reseauducommun/cociclo/cociclo_Mexico/hardware/circuit/cociclo_circuit imprimé.jpg

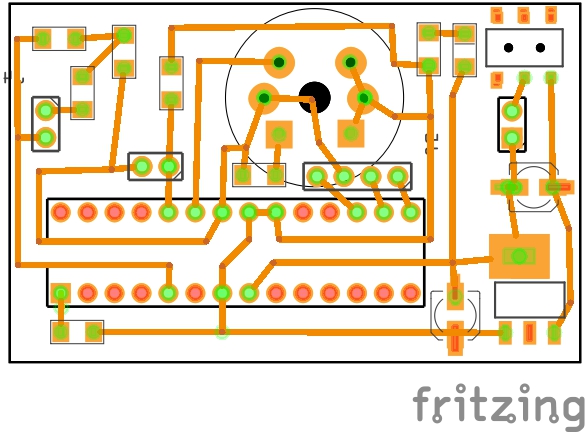
cociclo_Mexico/hardware/circuit/cociclo_circuit imprimé.jpg
