reseauducommun/cociclo/cociclo_transpiksel_eastern_bloc/cociclo_point_acces_EN.pdf

1. Go to:

http://fr.mygeoposition.com/

and note your position (latitude + longitude)

2. Power your cociclo
3. Log in to the 'cociclo' access point, the password is 'placecommune'

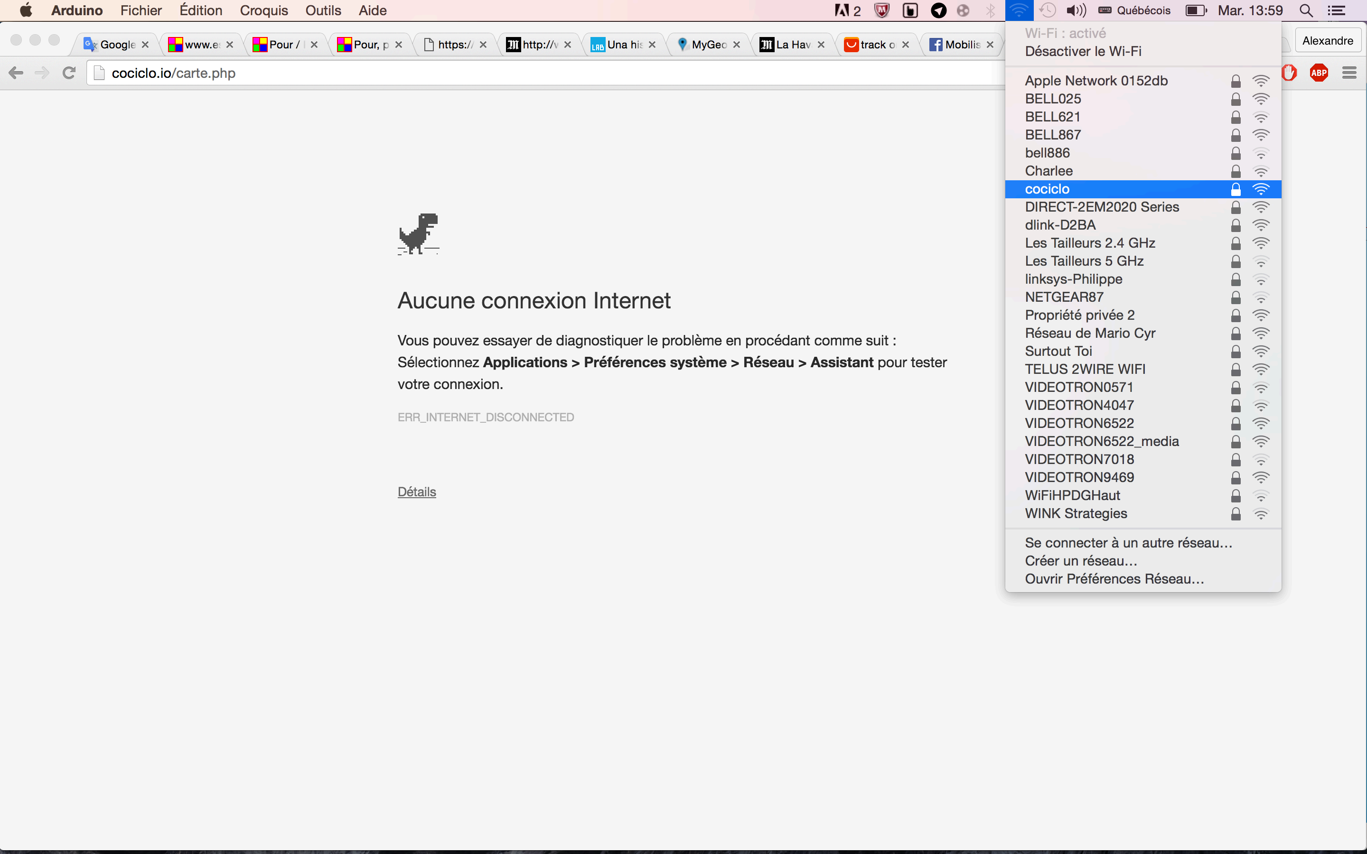
[picture p3: figure]

4. Open a new web page or enter this address : 192.168.4.1. Choose ‘Configure WIFI’ :

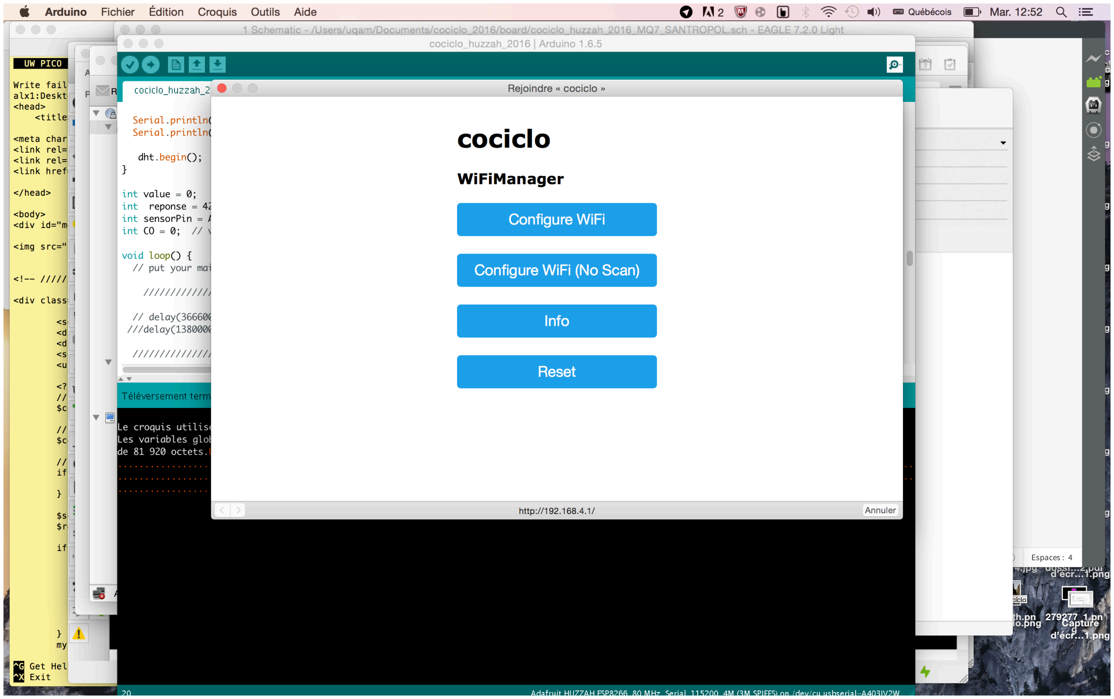
[picture p4: figure]

5. Select your home access point and enter your password, choose a name for your cociclo (no special characters or spaces) the latitude and longitude of your cociclo.

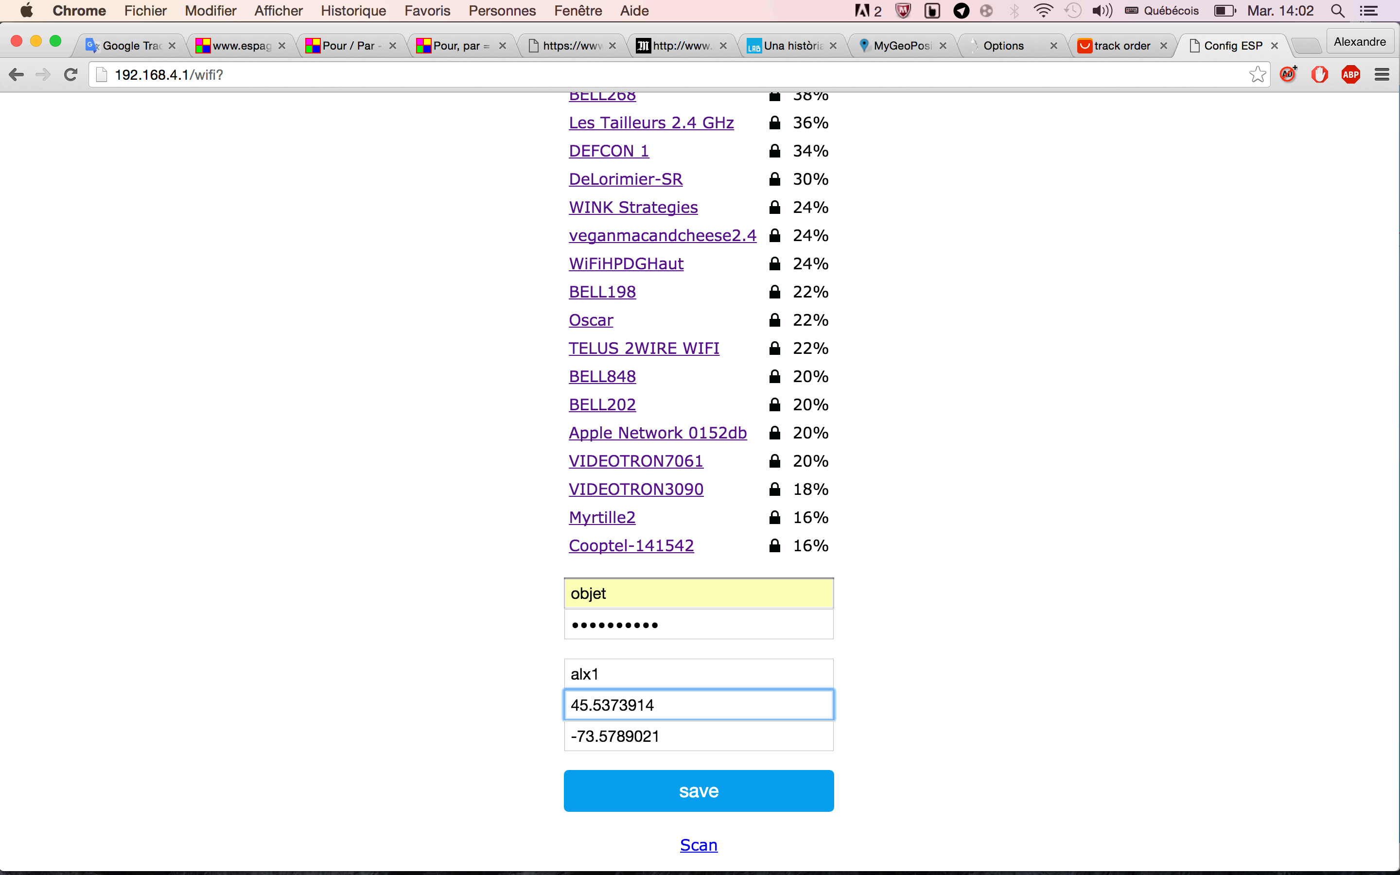
[picture p5: figure]

6. Restart your cociclo
7. Wait for 25 minutes (to heat the CO sensor and avoid false readings) skip this point if the cociclo is not configured with this long pause.
8. Go to http://cociclo.io/carte.php and see your cocíclo on the map.
9. Send an image of your installation.

If there’s a problem, send a mail to : acastonguay@artengine.ca
