reseauducommun/cociclo/cociclo_Mexico/hardware/mexico/cociclo_mexico_etch_silk_top.pdf

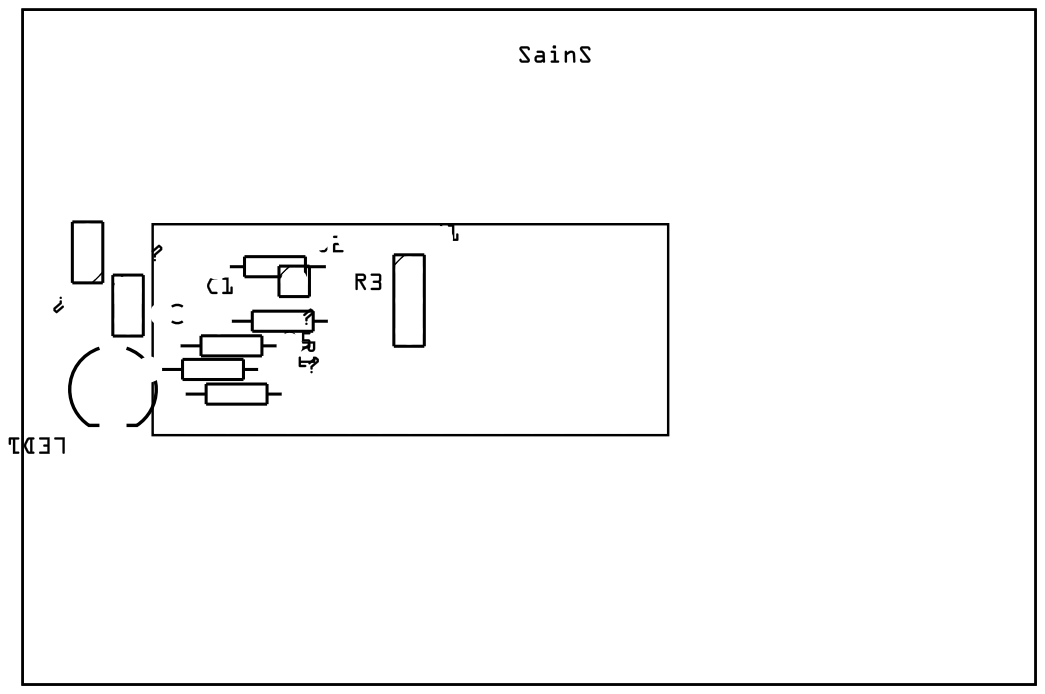
[picture p6: page 1]
