reseauducommun/cociclo/cociclo_Mexico/hardware/mexico/cociclo_mexico_etch_silk_top_mirror.pdf

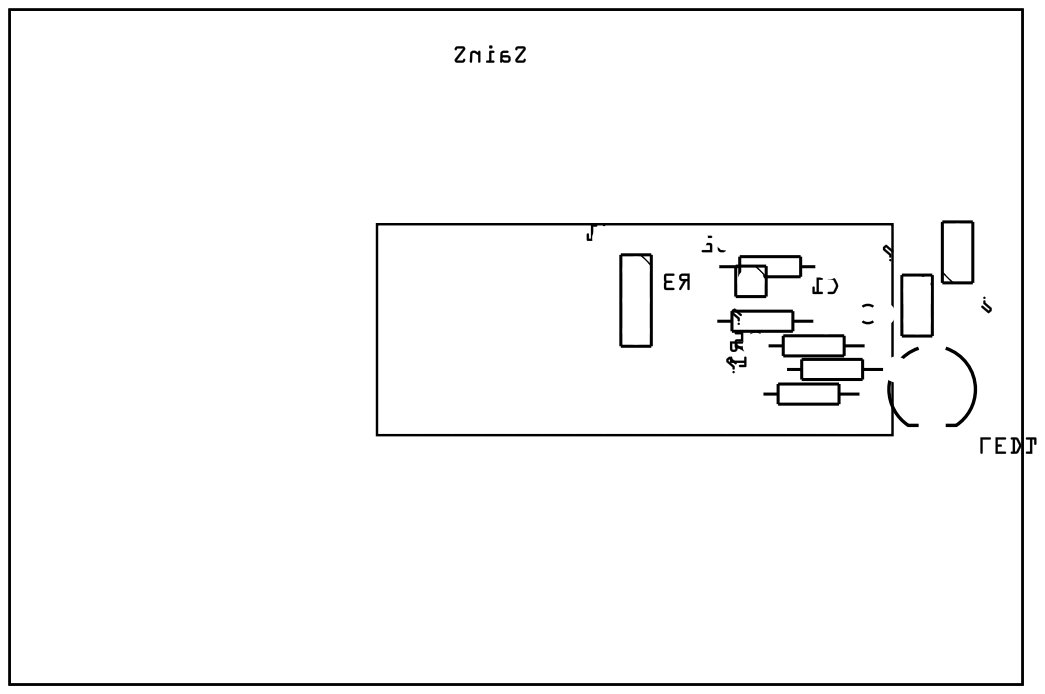
[picture p7: page 1]
