reseauducommun/cociclo/cociclo_Mexico/hardware/circuit/hey/cociclo_etch_paste_mask_bottom.pdf

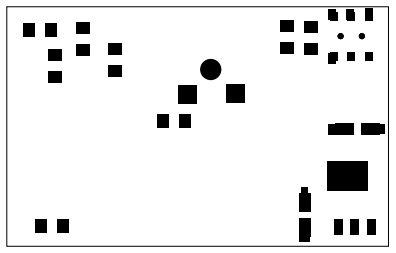
[picture p8: figure]
