reseauducommun/cociclo/cociclo_Mexico/hardware/circuit/hey/cociclo_etch_paste_mask_bottom_mirror.pdf

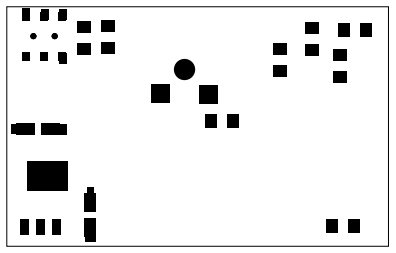
[picture p9: figure]
