reseauducommun/cociclo/cociclo_Mexico/hardware/mexico/mexicoDF/cociclo_mexico_etch_silk_top.pdf

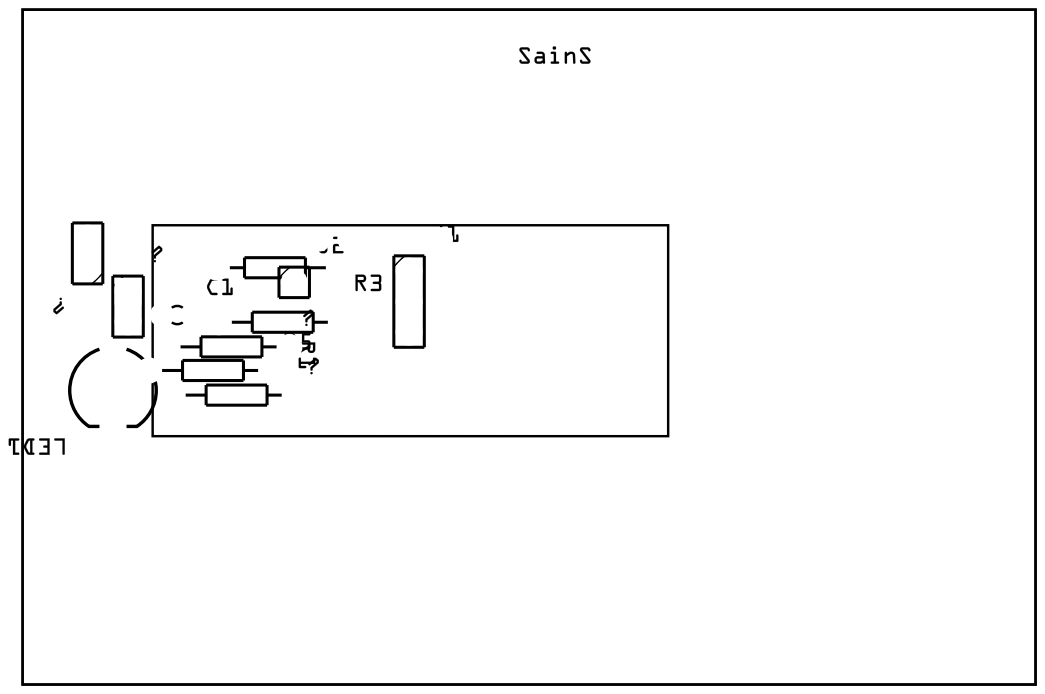
[picture p10: page 1]
