reseauducommun/cociclo/cociclo_Mexico/hardware/mexico/mexicoDF/cociclo_mexico_etch_silk_top_mirror.pdf

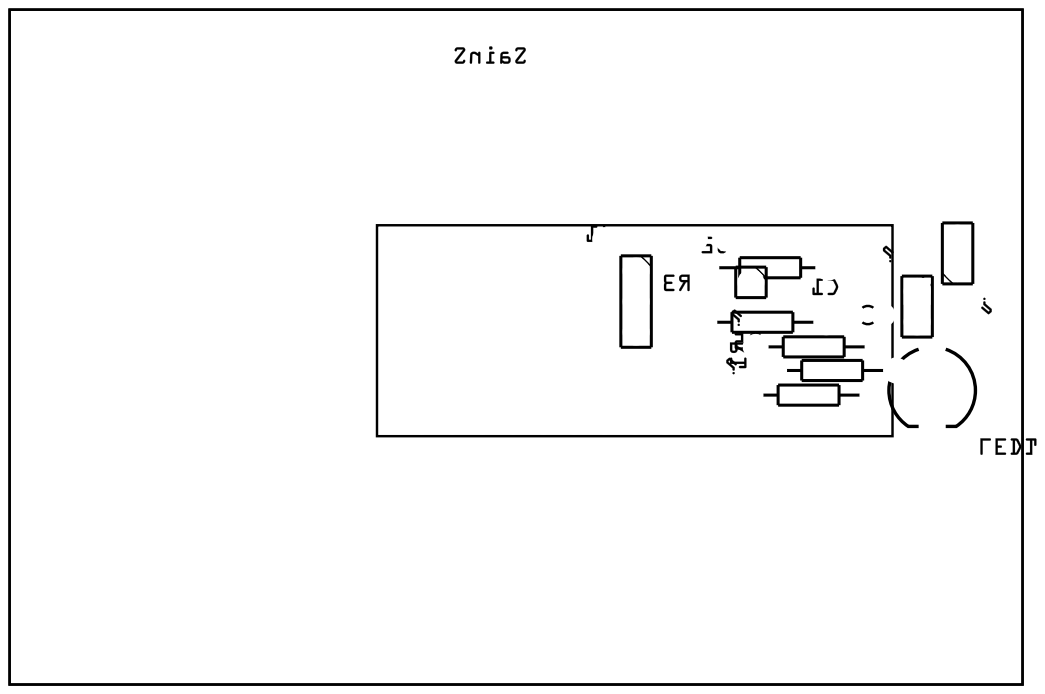
[picture p11: page 1]
