reseauducommun/cociclo/cociclo_placeCommune/software/cociclo_point_acces_p.pdf

1. Allez à':'

http://fr.mygeoposition.com/

et'notez'votre'position'

2. Branchez'votre'cocíclo'
3. Branchez votre'ordinateur'sur'le'point'd'accès''cociclo','le'mot'de passe'est''placecommune''

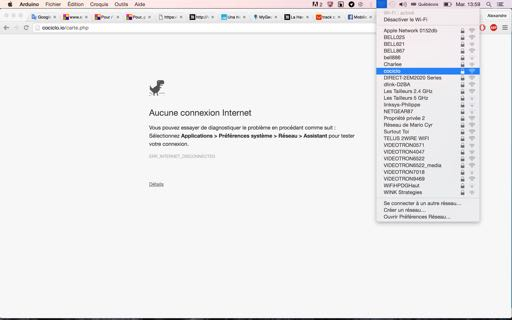
[picture p12: figure]

4.'Ouvrez'une'page'de'navigateur'et'allez'à'192.168.4.1'(ou tentez'd'accéder'à'n'importe'qu'elle'page).'Choisir' ‘Configure'WIFI’ :

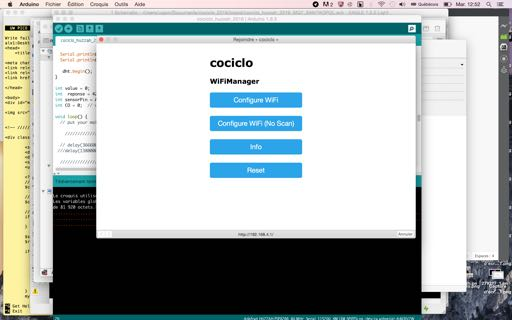
[picture p13: figure]

5.'Choisissez'un'nom'd'utilisateur,'entrez'votre'nom'de'point'd'accès'au'réseau'et'son'mot'de'passe'ainsi'que' la'latitude'et'la'longitude'de'la'position'de'votre'cocíclo.

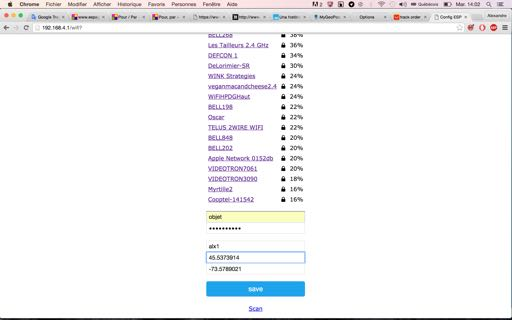
[picture p14: figure]

6.'Redémarrez'votre'cocíclo'

7.'Patientez 25'minutes (le'temps'de'réchauffer'le'capteur'de'CO'afin'd’éviter'les'mauvaises'lectures,'allez'à'la' page'http://cociclo.io/carte.php et'trouvez'les'valeurs'de'votre'cocíclo'

8.'Postez'une'image'de'l'endroit'où'vous'avez'installé'votre'cocíclo.'

En'cas'de'problème,'contactezYmoi'à'acastonguay@artengine.ca
