reseauducommun/cociclo/cociclo_03/hardware/eagleUp/01/eagleUp_cociclo_03_top_silk.png

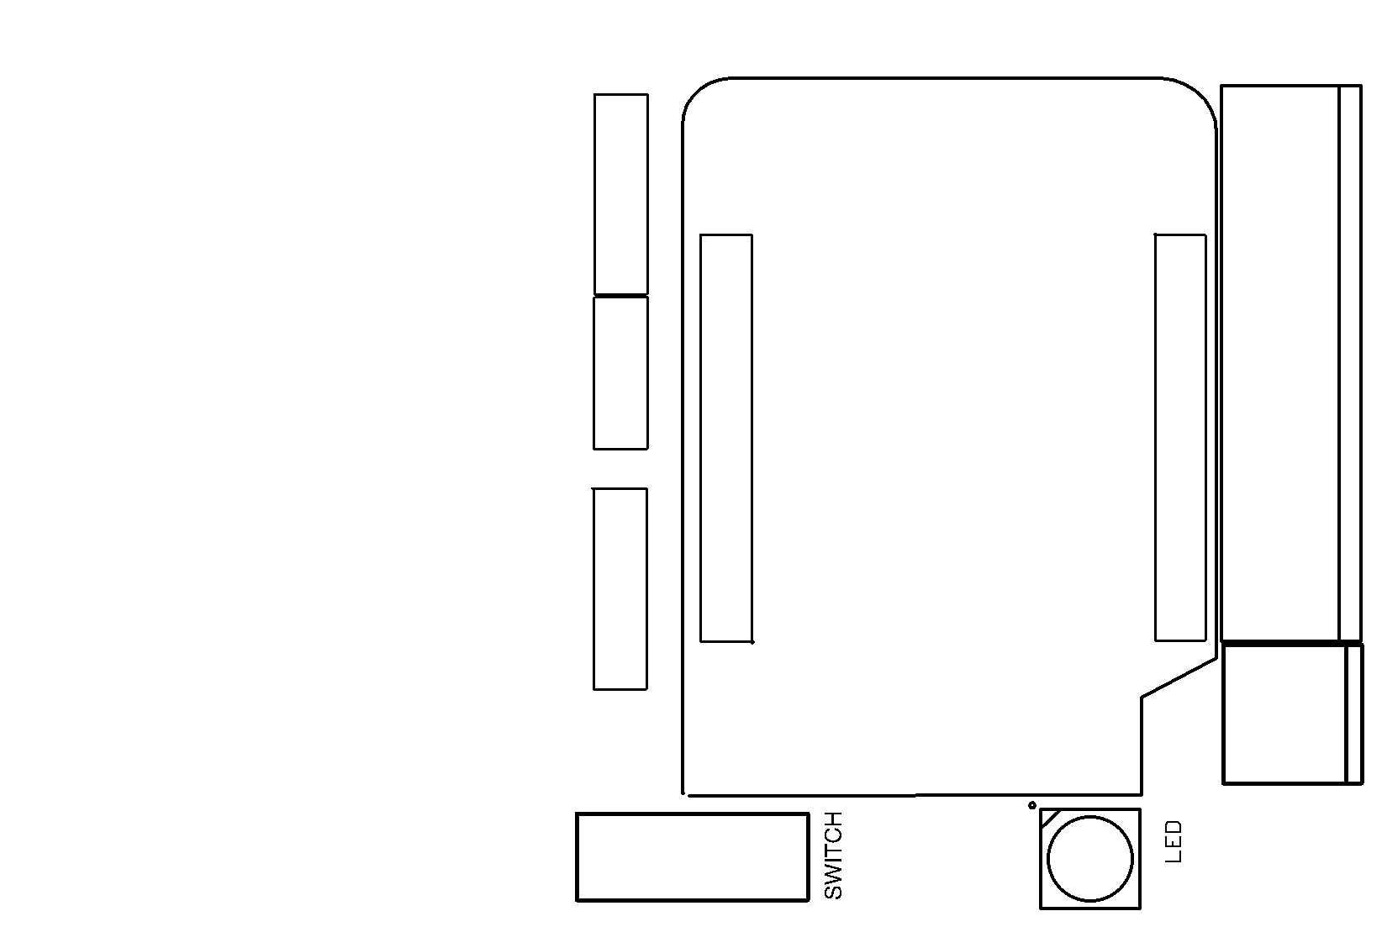
cociclo_03/hardware/eagleUp/01/eagleUp_cociclo_03_top_silk.png
