reseauducommun/cociclo/cociclo_03/hardware/PMS3003_connections.png

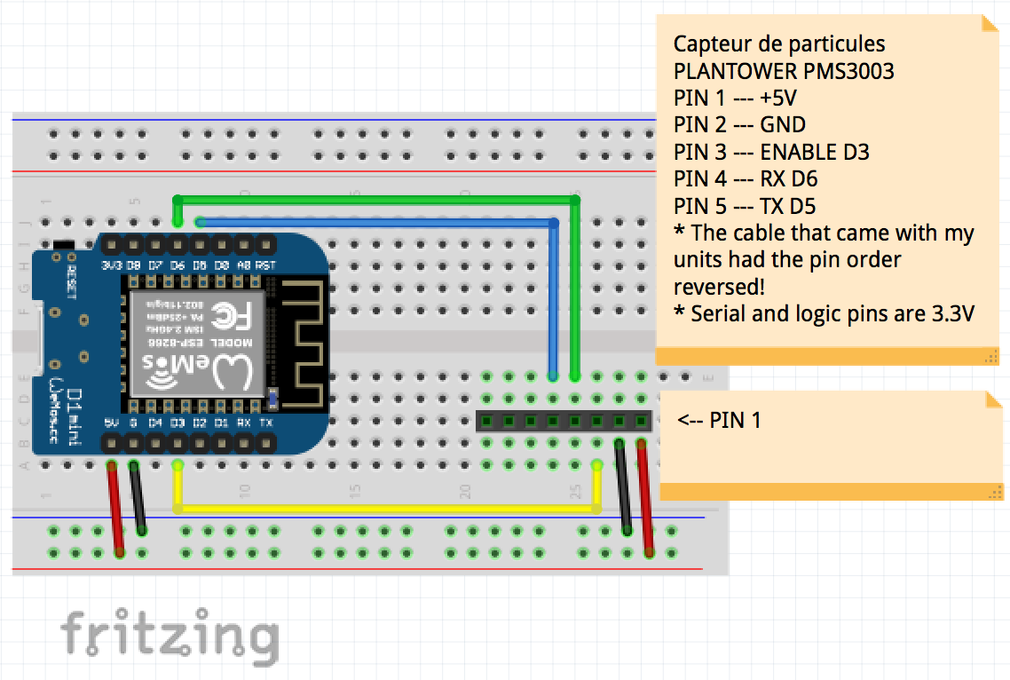
cociclo_03/hardware/PMS3003_connections.png
