reseauducommun/cociclo/cociclo_03/images/cociclo_0_3.jpg

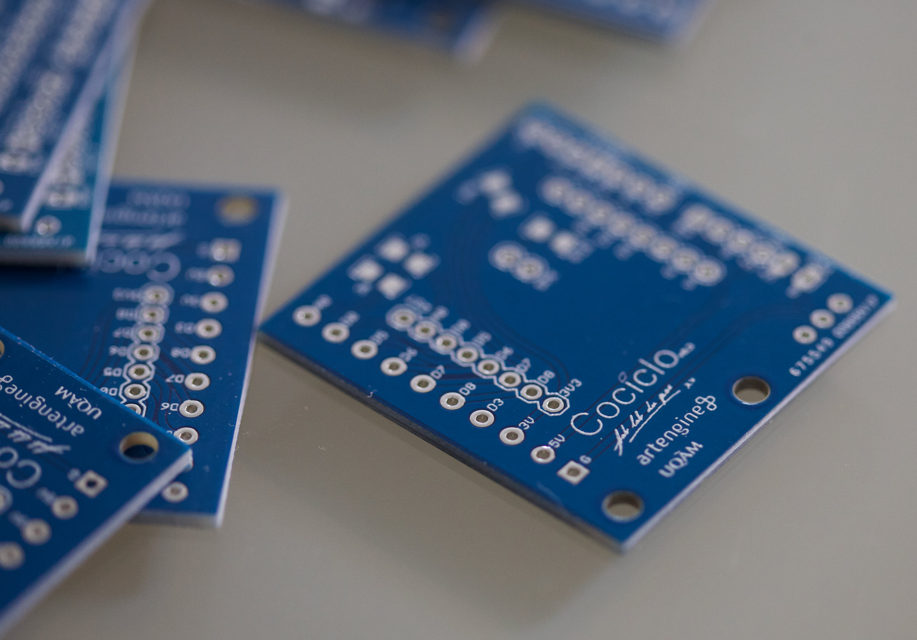
cociclo_03/images/cociclo_0_3.jpg
