reseauducommun/cociclo/cociclo_03/images/eagle_board_capture.png

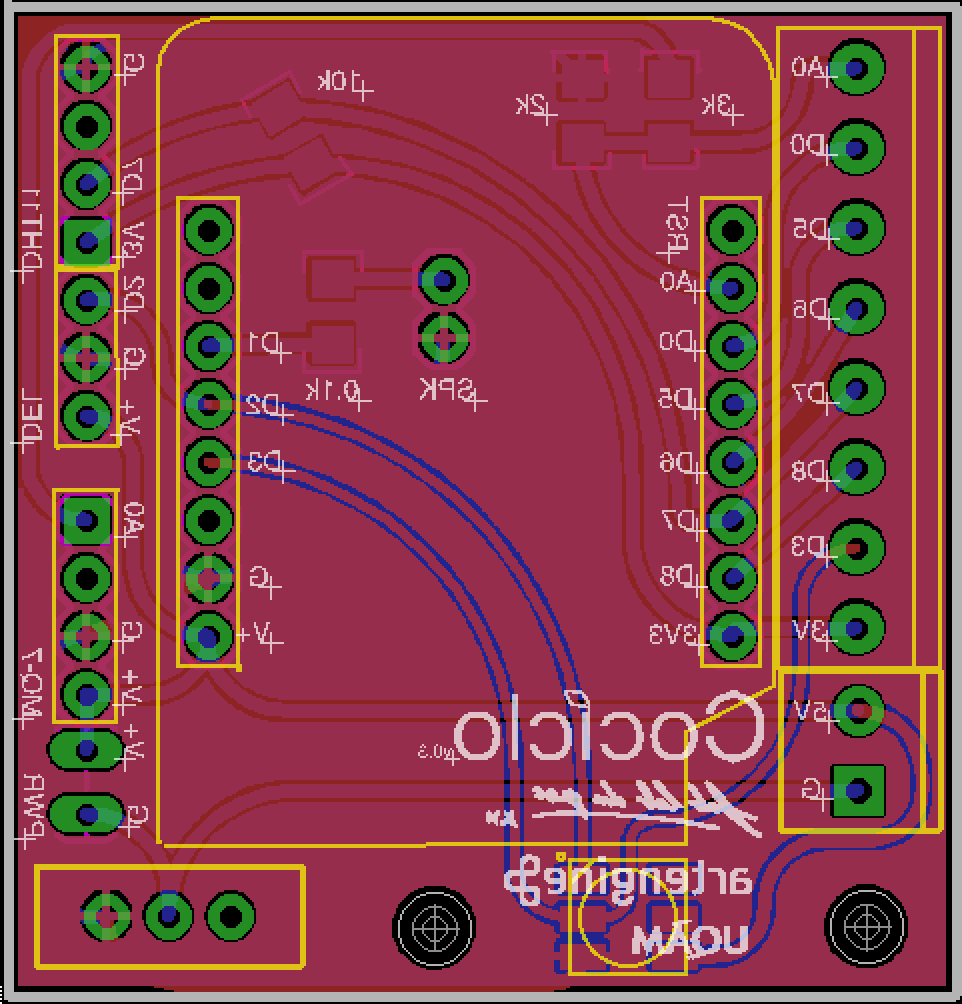
cociclo_03/images/eagle_board_capture.png
