reseauducommun/cociclo/cociclo_cordova/platforms/android/assets/www/img/submerge.png

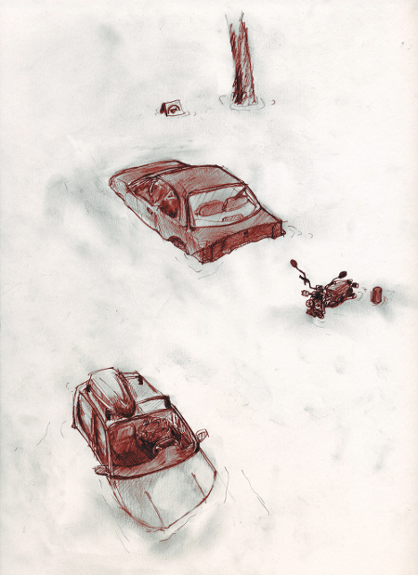
cociclo_cordova/platforms/android/assets/www/img/submerge.png
