reseauducommun/cociclo/cociclo_flowchart.png

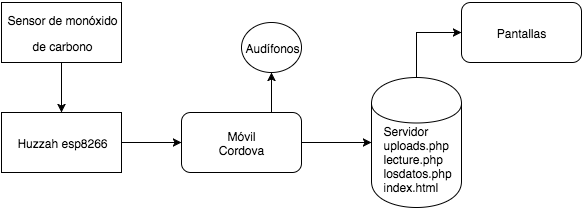
cociclo_flowchart.png
