reseauducommun/cociclo/cociclo_hardware/cociclo_bergen_stencil.png

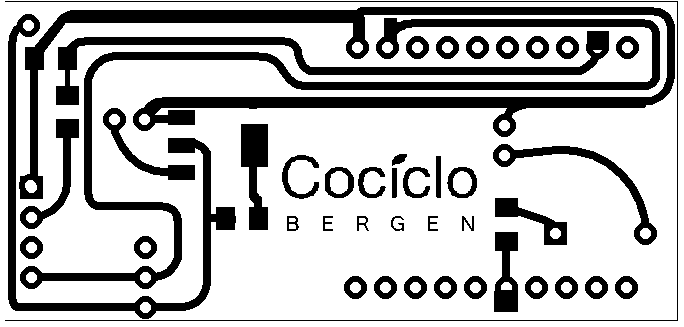
cociclo_hardware/cociclo_bergen_stencil.png
