reseauducommun/cociclo/cociclo_Mexico/hardware/instructions/CTIA_OMTP_Pinout_thumb.png

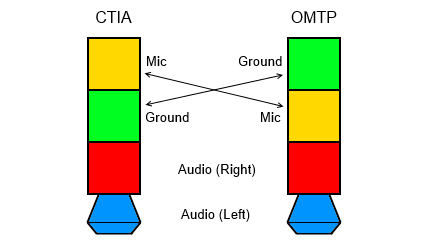
cociclo_Mexico/hardware/instructions/CTIA_OMTP_Pinout_thumb.png
