reseauducommun/cociclo/cociclo_placeCommune/boitier/fond_cociclo_wemos.jpg

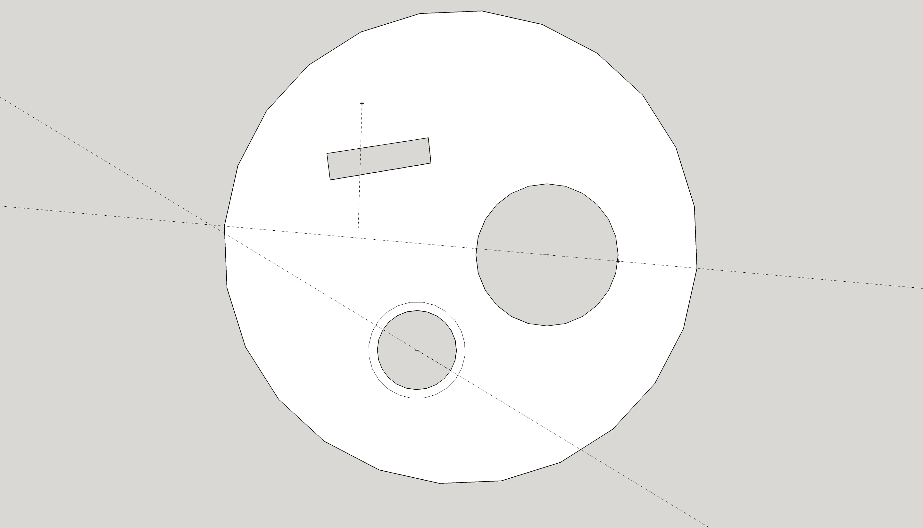
cociclo_placeCommune/boitier/fond_cociclo_wemos.jpg
