reseauducommun/cociclo/cociclo_placeCommune/hardware/cociclo_2016.png

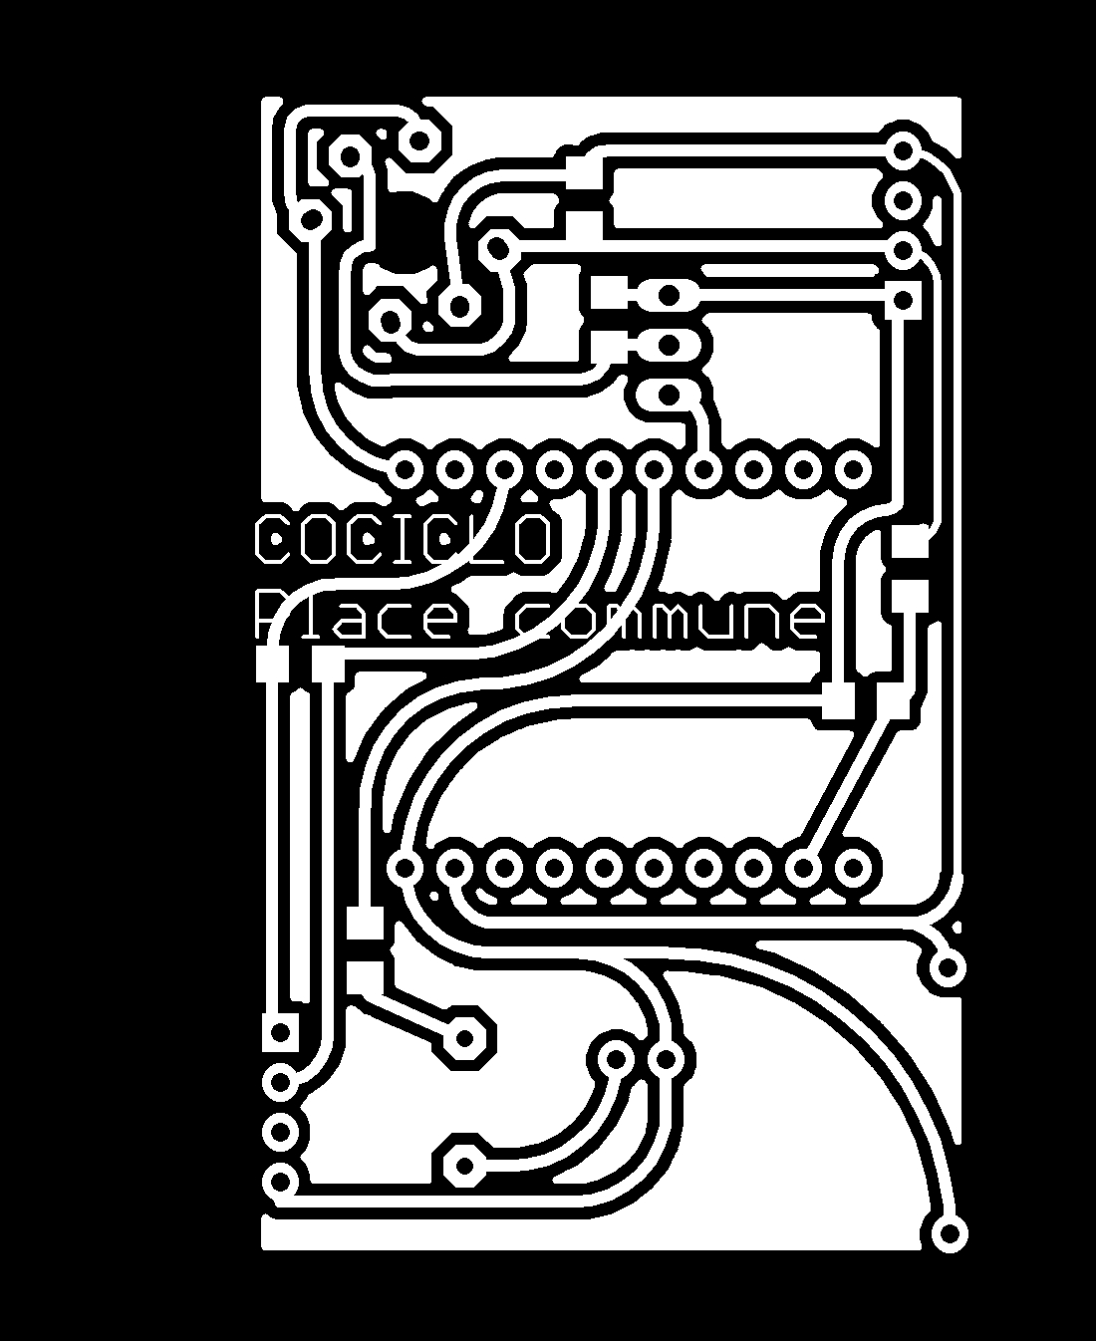
cociclo_placeCommune/hardware/cociclo_2016.png
