reseauducommun/cociclo/cociclo_placeCommune/hardware/cociclo_plaeCommune_composantes.png

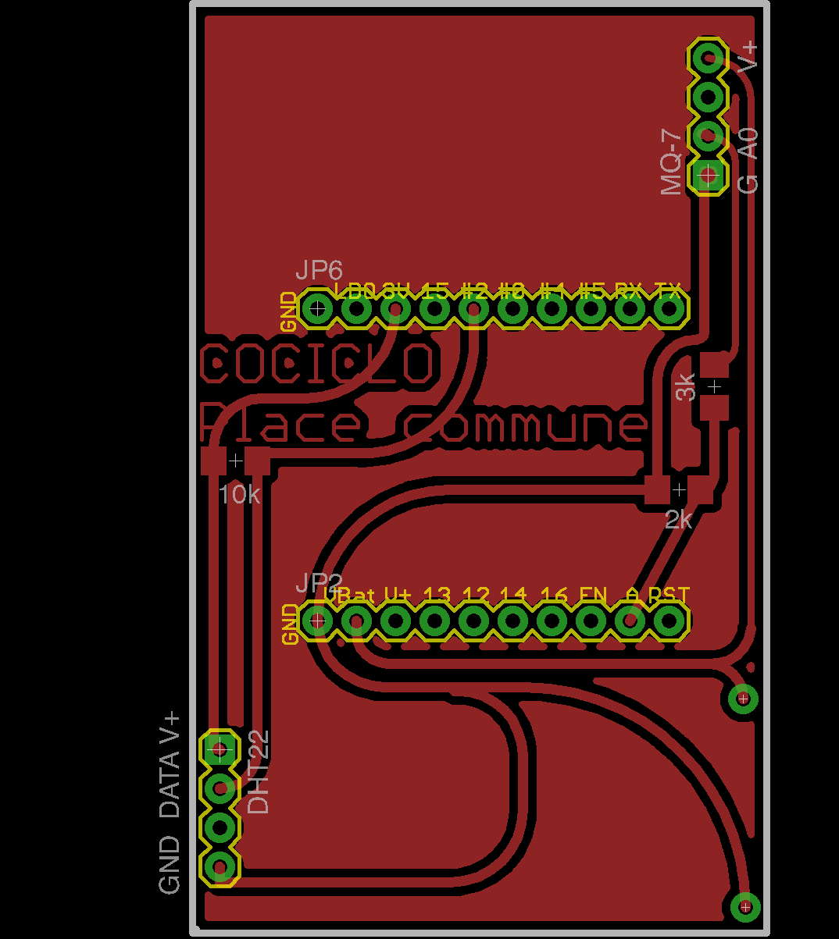
cociclo_placeCommune/hardware/cociclo_plaeCommune_composantes.png
