reseauducommun/cociclo/cociclo_placeCommune/hardware/sainsmart_MQ7.jpg

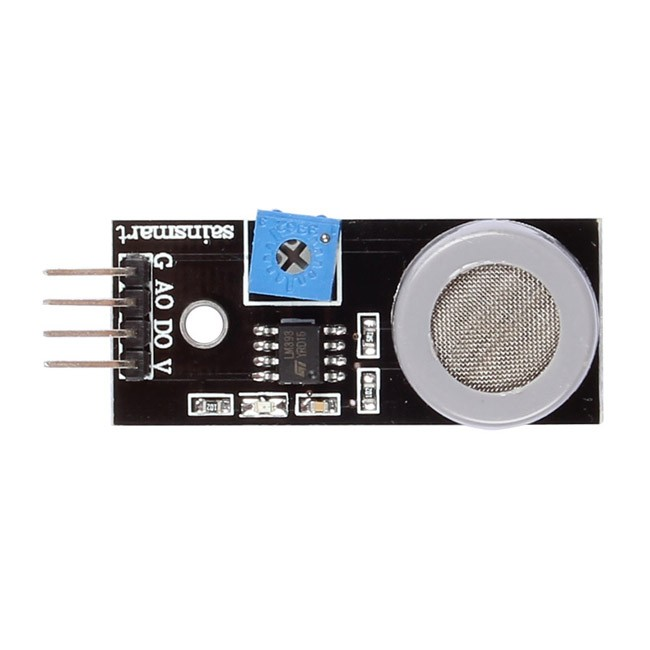
cociclo_placeCommune/hardware/sainsmart_MQ7.jpg
