reseauducommun/cociclo/cociclo_Mexico/hardware/instructions/instructions.pdf

Cocíclo v.

0.42

(Cali

noviembre

2014)

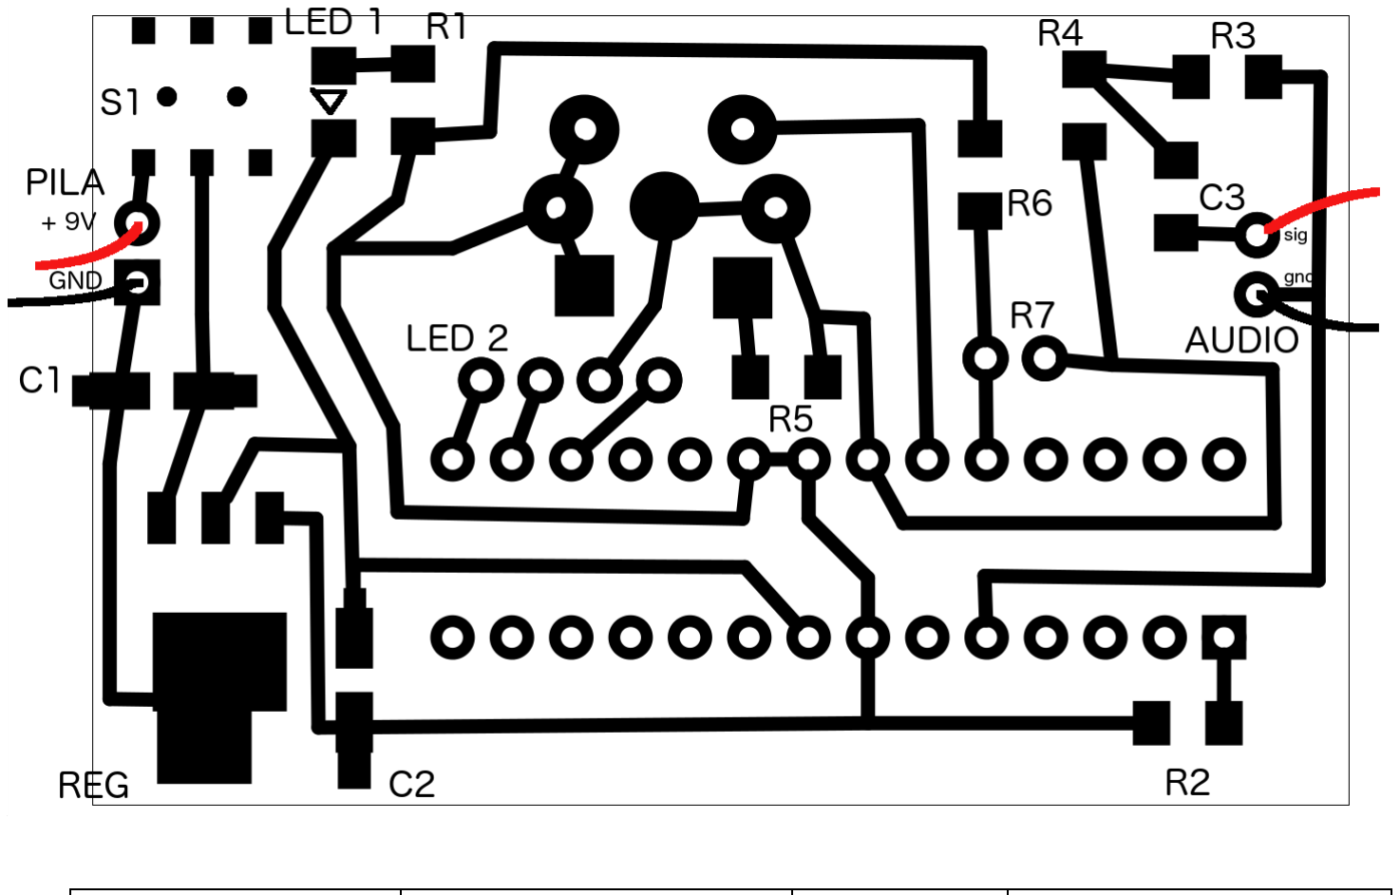
[picture p40: figure]

Identifiant | Type | Valor | Digikey part #
R1 | Resistencia | 330 ohms
R2, R3, R5 | Resistencias | 10k ohms
R4 | Resistencia | 390 ohms
C1,C2 | Condensatores | 10 uF
C3 | Condensatore | 1 nf
LED 1 | LED | indicator
LED2 | LED through hole | tri-‐color
REG | Regulatore de tension | 5V
S1 | Interruptor
Pila | Cable | 9V
Audio | Cable | audio
Barquetta | 28 pins
ATMEGA168PU | Microcontroler
MH-‐7 | Capteur | CO
Opcional
R6 | resistancia | 10k ohms
R7 | Photoresistor | 2-‐80k ohms

Cocíclo v.

0.42

(Cali

noviembre

2014)
