reseauducommun/cociclo/cociclo_Mexico/hardware/instructions/ciclo_bottom.png

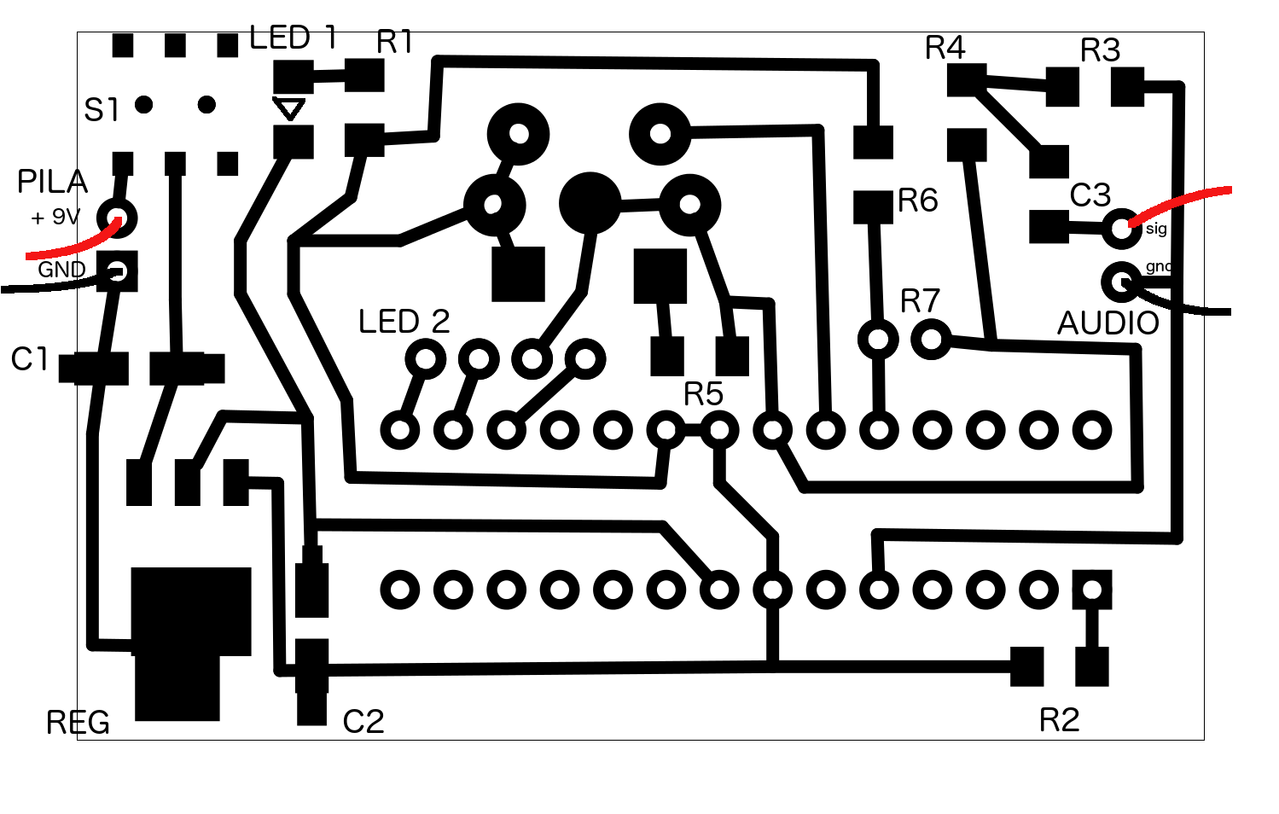
cociclo_Mexico/hardware/instructions/ciclo_bottom.png
