reseauducommun/cociclo/cociclo_Mexico/hardware/mexico/cociclo_mexico_etch_silk_bottom.pdf

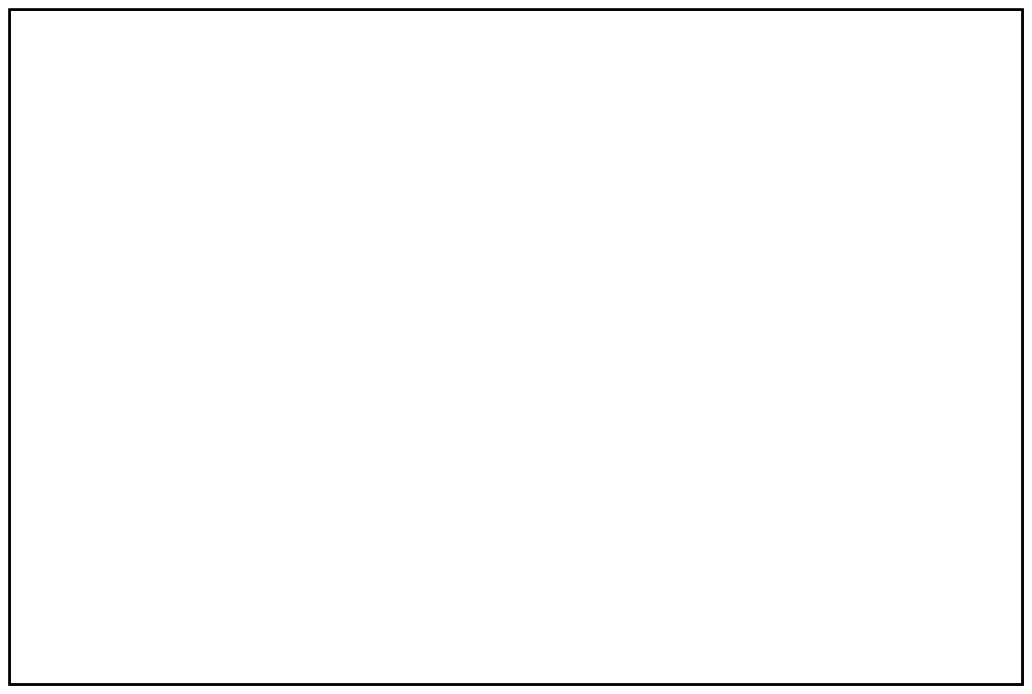
[picture p55: page 1]
