reseauducommun/cociclo/cociclo_Mexico/hardware/circuit/cociclo_etch_mask_bottom_mirror.pdf

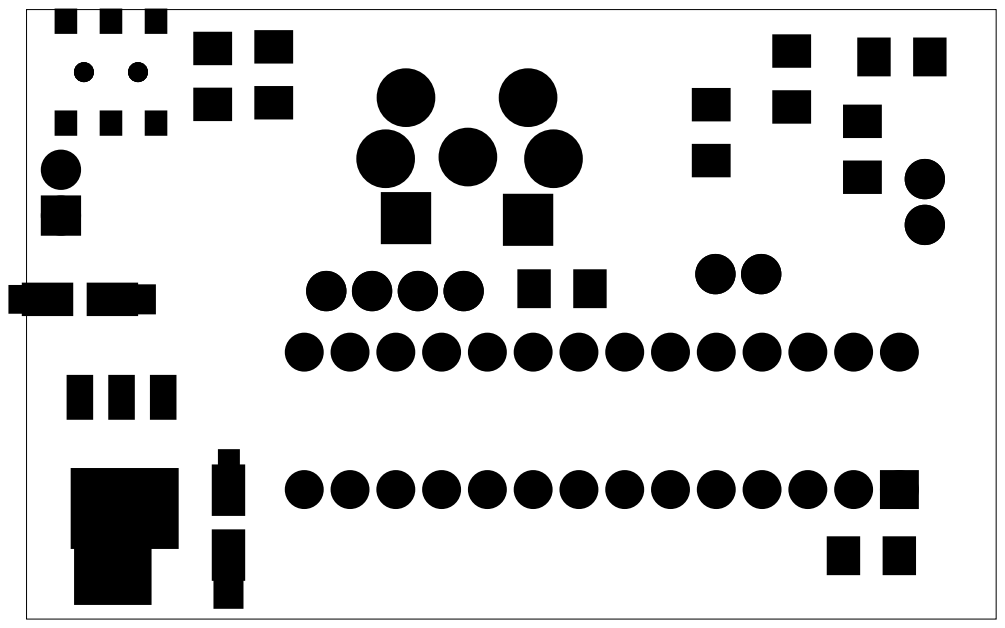
[picture p56: page 1]
