reseauducommun/cociclo/cociclo_Mexico/hardware/circuit/hey/cociclo_etch_copper_bottom.pdf

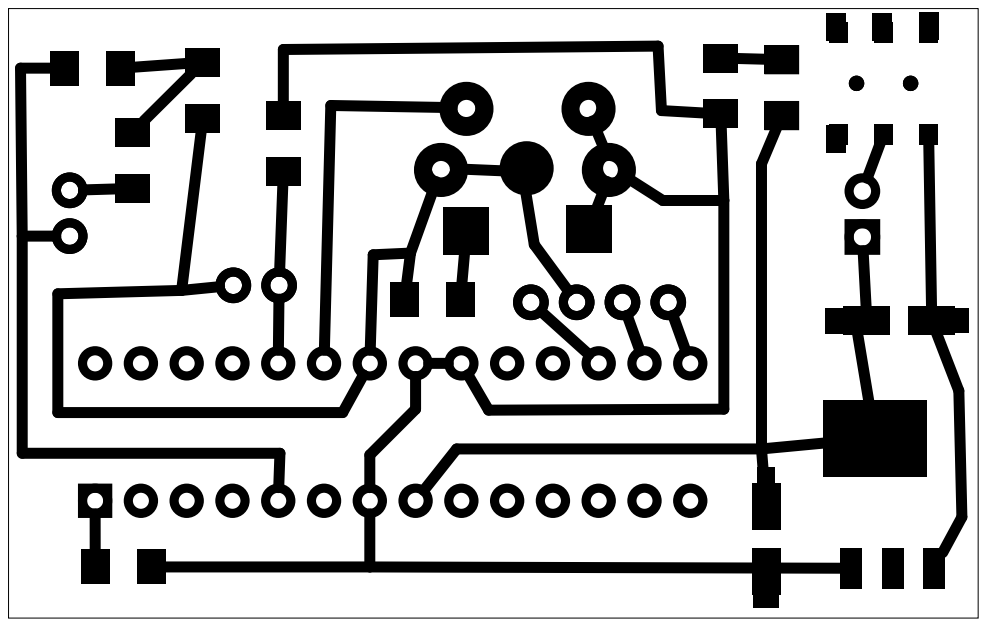
[picture p57: page 1]
