reseauducommun/cociclo/cociclo_Mexico/hardware/circuit/hey/cociclo_etch_copper_bottom_mirror.pdf

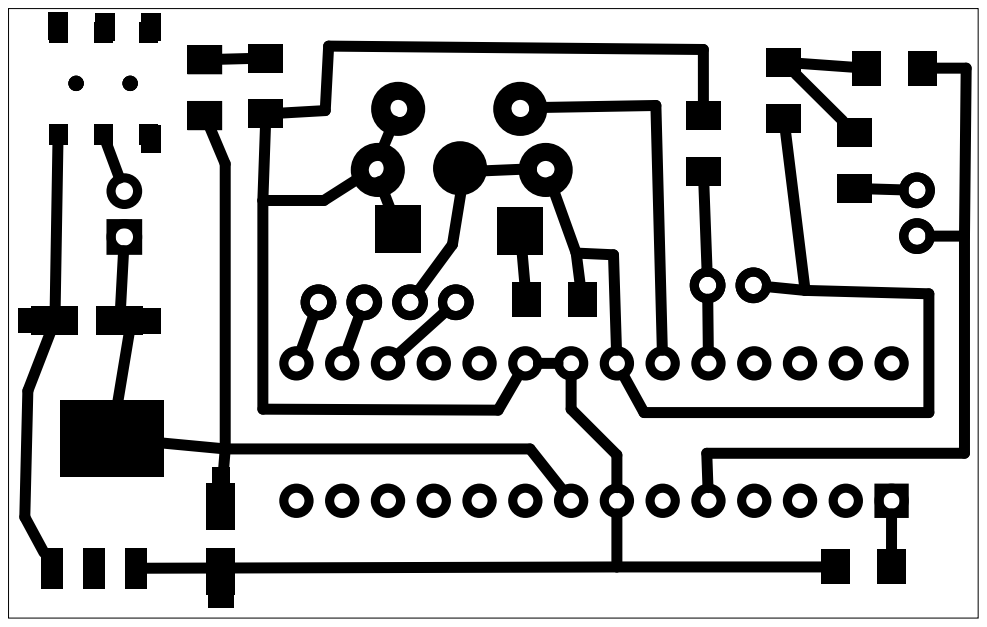
[picture p58: page 1]
