reseauducommun/cociclo/cociclo_Mexico/hardware/circuit/hey/cociclo_etch_copper_top.pdf

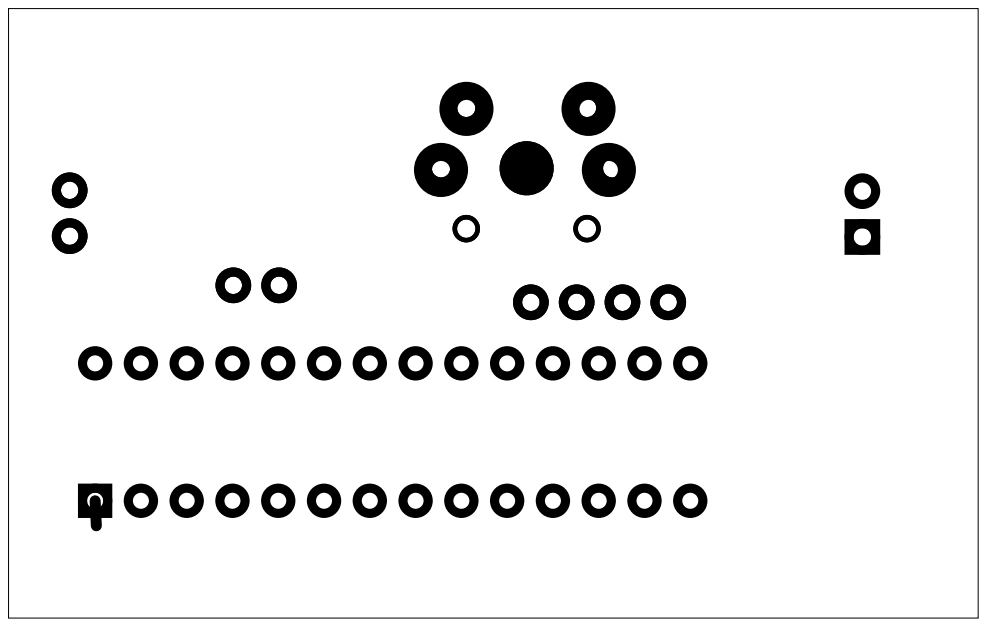
[picture p59: page 1]
