reseauducommun/cociclo/cociclo_Mexico/hardware/circuit/hey/cociclo_etch_copper_top_mirror.pdf

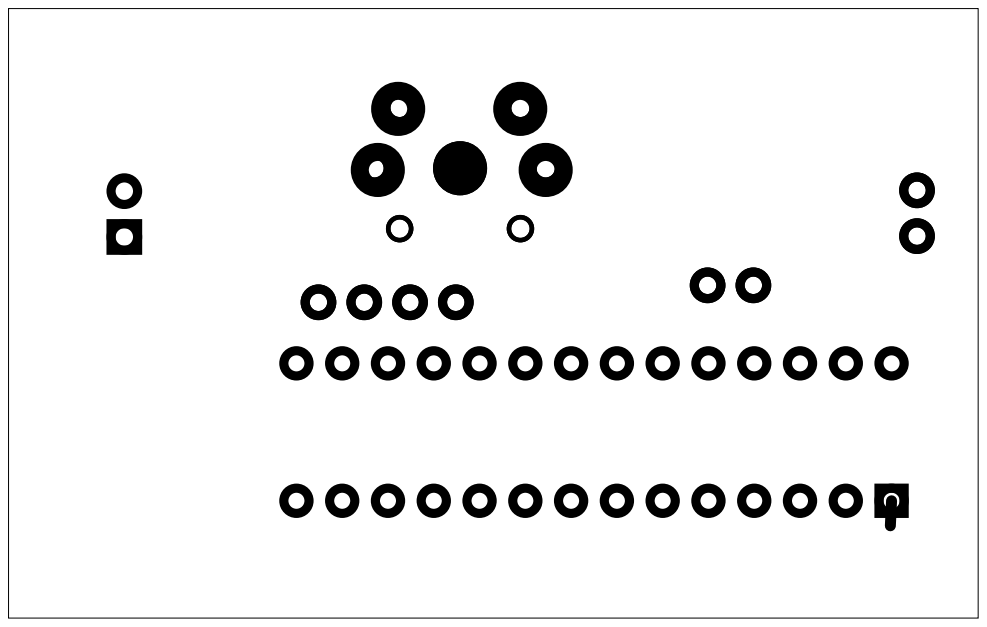
[picture p60: page 1]
