reseauducommun/cociclo/cociclo_Mexico/hardware/circuit/hey/cociclo_etch_mask_bottom.pdf

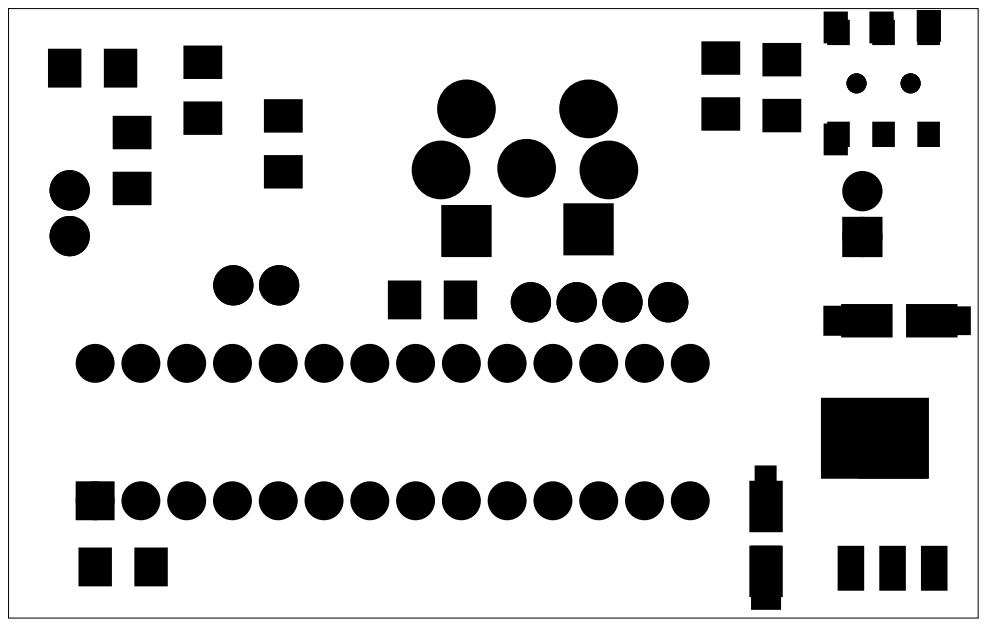
[picture p61: page 1]
