reseauducommun/cociclo/cociclo_Mexico/hardware/circuit/hey/cociclo_etch_mask_bottom_mirror.pdf

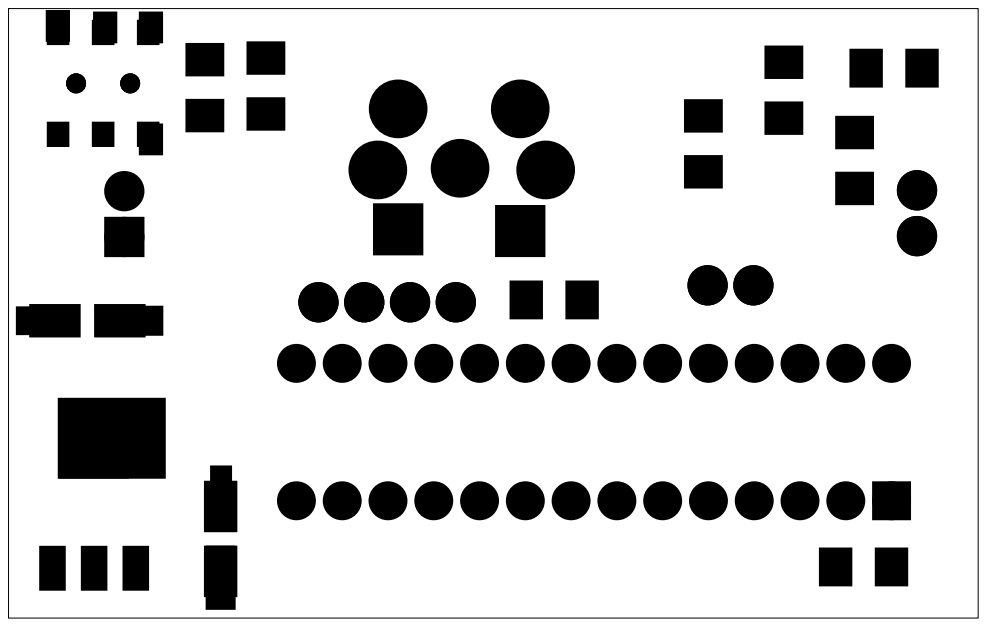
[picture p62: page 1]
