reseauducommun/cociclo/cociclo_Mexico/hardware/circuit/hey/cociclo_etch_mask_top.pdf

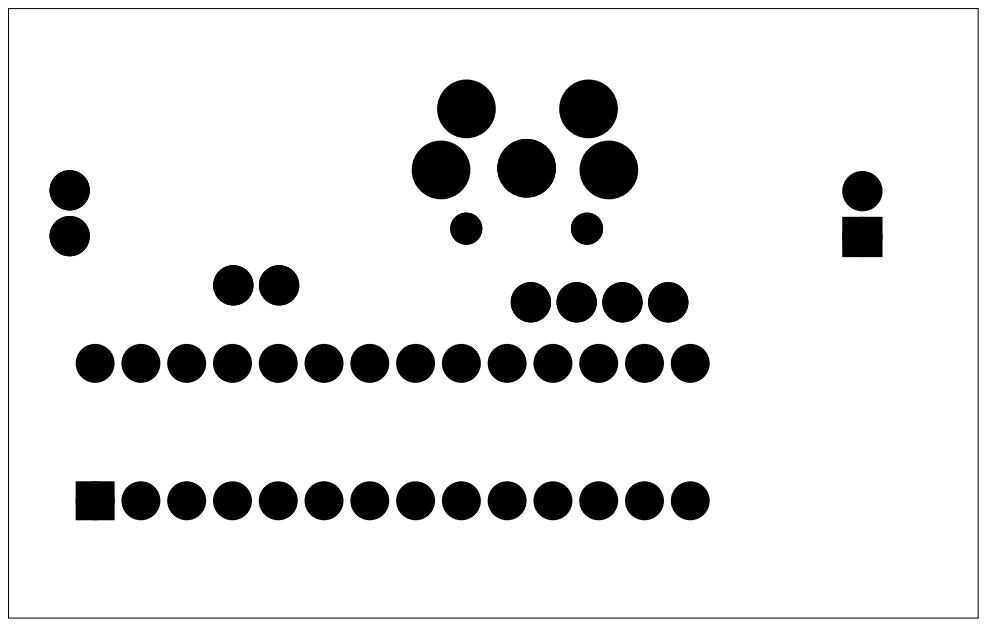
[picture p63: page 1]
