reseauducommun/cociclo/cociclo_Mexico/hardware/circuit/hey/cociclo_etch_mask_top_mirror.pdf

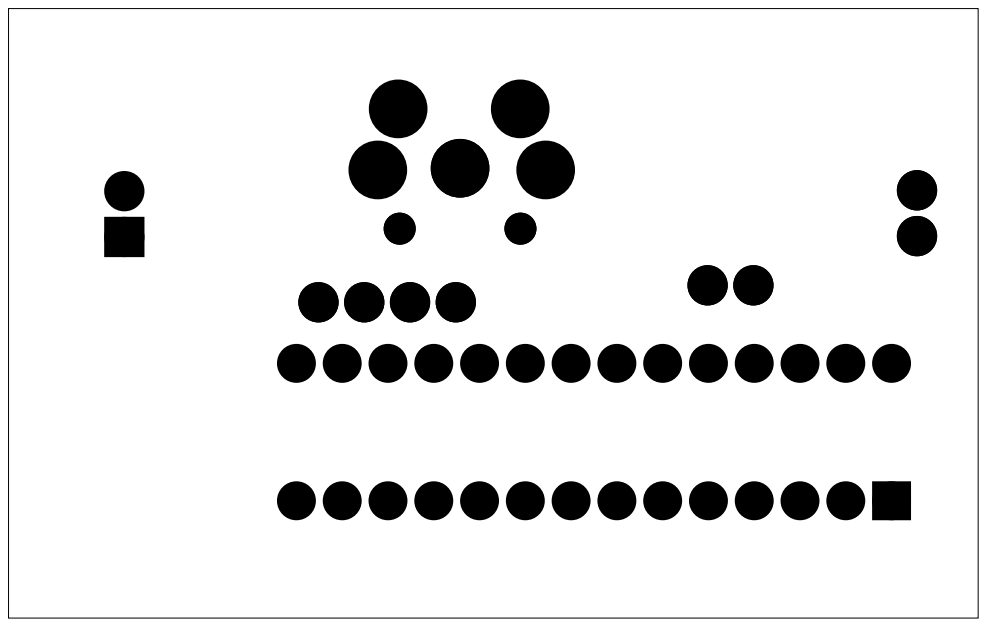
[picture p64: page 1]
