reseauducommun/cociclo/cociclo_Mexico/hardware/circuit/hey/cociclo_etch_silk_bottom.pdf

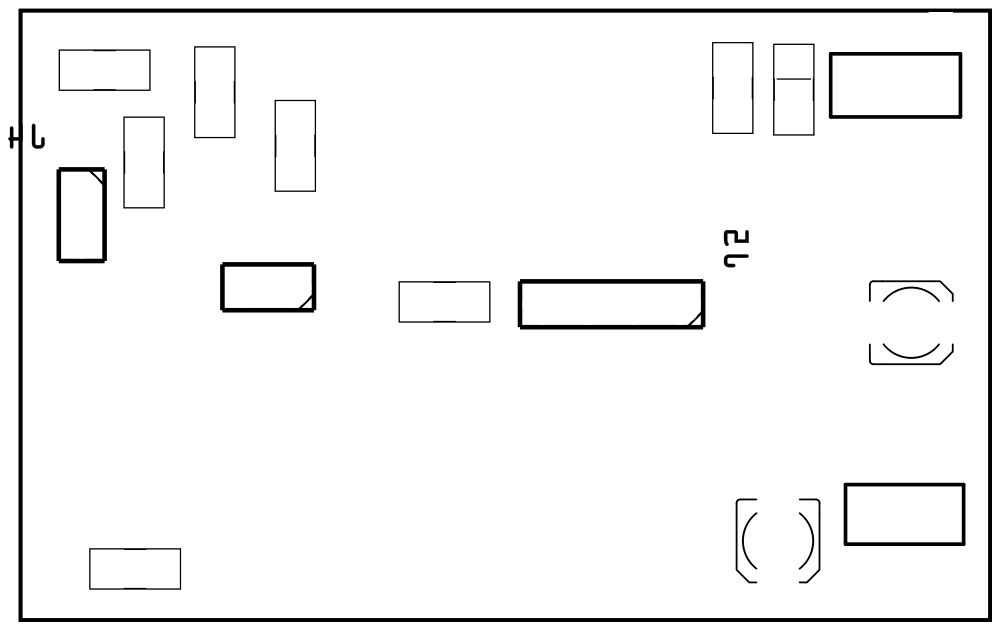
[picture p65: page 1]
