reseauducommun/cociclo/cociclo_Mexico/hardware/circuit/hey/cociclo_etch_silk_bottom_mirror.pdf

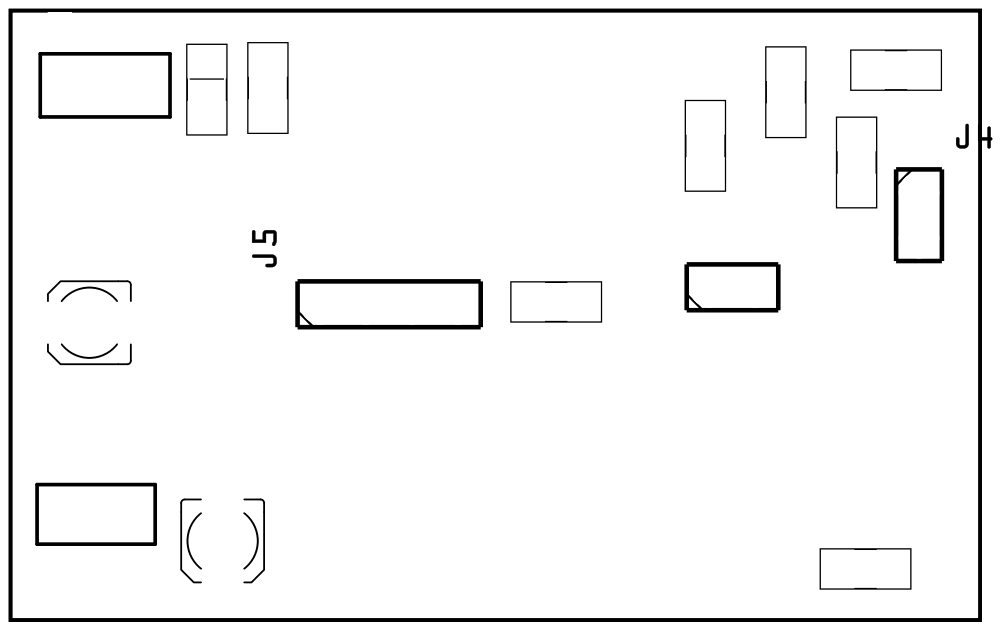
[picture p66: page 1]
