reseauducommun/cociclo/cociclo_Mexico/hardware/circuit/hey/cociclo_etch_silk_top.pdf

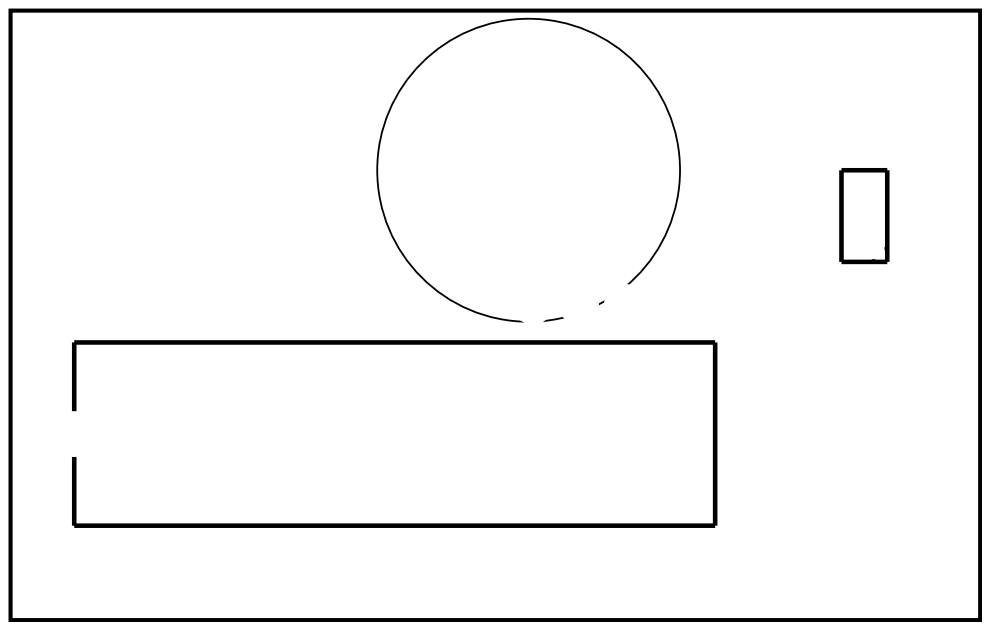
[picture p67: page 1]
