reseauducommun/cociclo/cociclo_Mexico/hardware/circuit/hey/cociclo_etch_silk_top_mirror.pdf

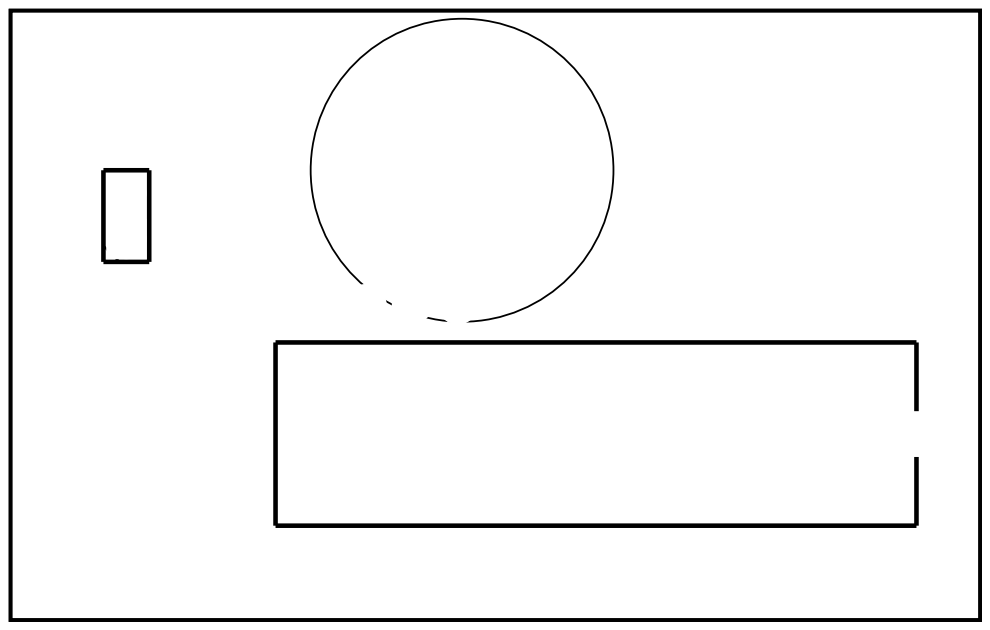
[picture p68: page 1]
