reseauducommun/cociclo/cociclo_Mexico/hardware/mexico/mexicoDF/cociclo_mexico_etch_copper_bottom.pdf

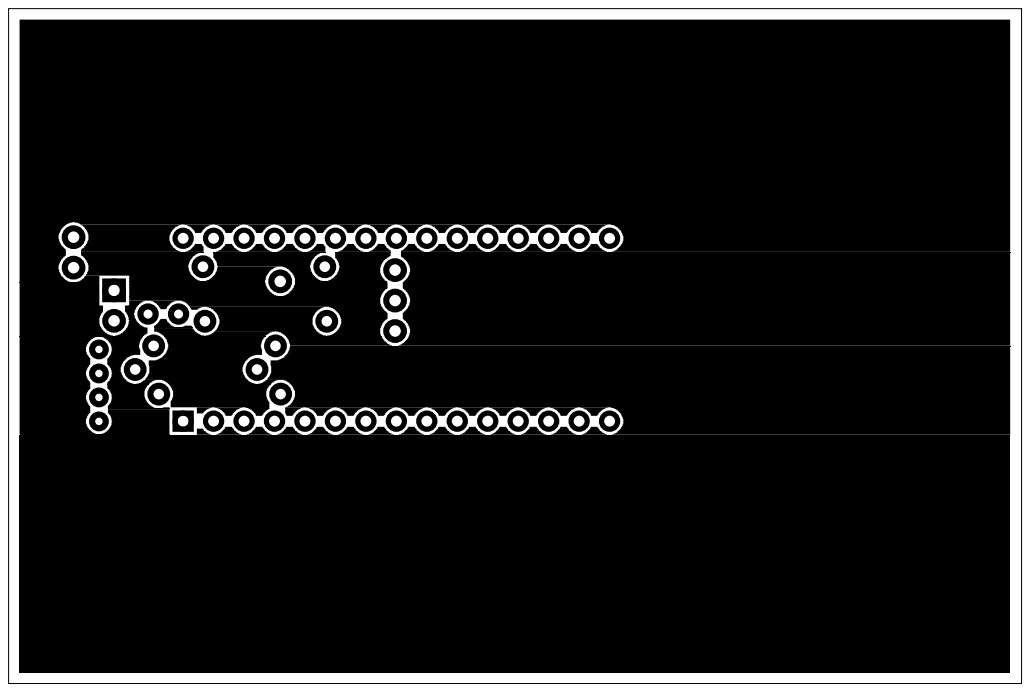
[picture p69: page 1]
