reseauducommun/cociclo/cociclo_Mexico/hardware/mexico/mexicoDF/cociclo_mexico_etch_copper_bottom_mirror.pdf

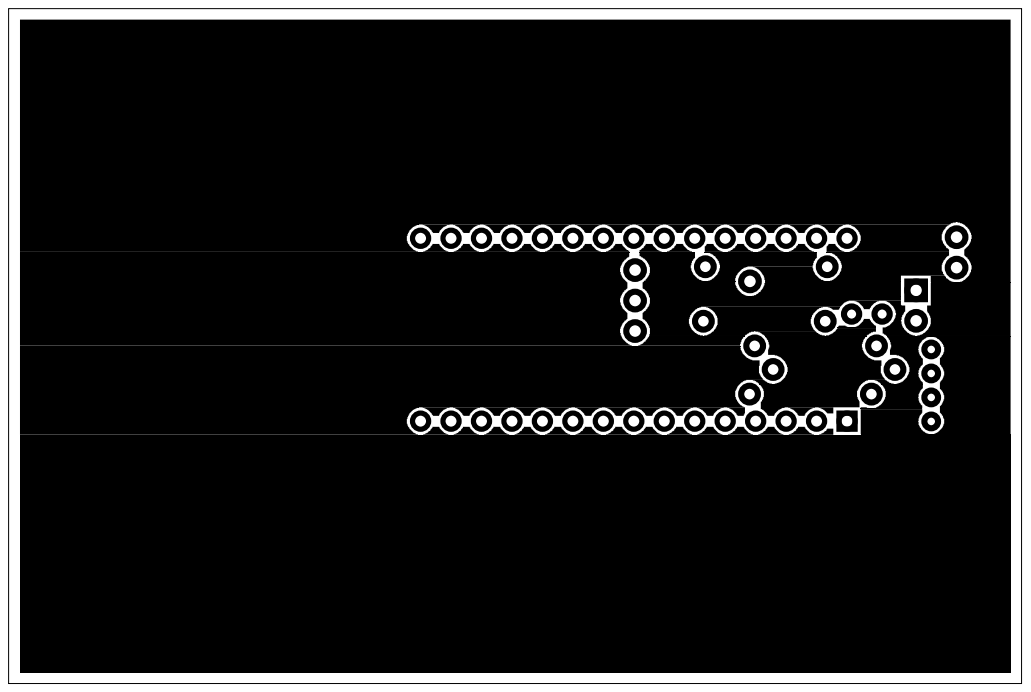
[picture p70: page 1]
