reseauducommun/cociclo/cociclo_Mexico/hardware/mexico/mexicoDF/cociclo_mexico_etch_copper_top.pdf

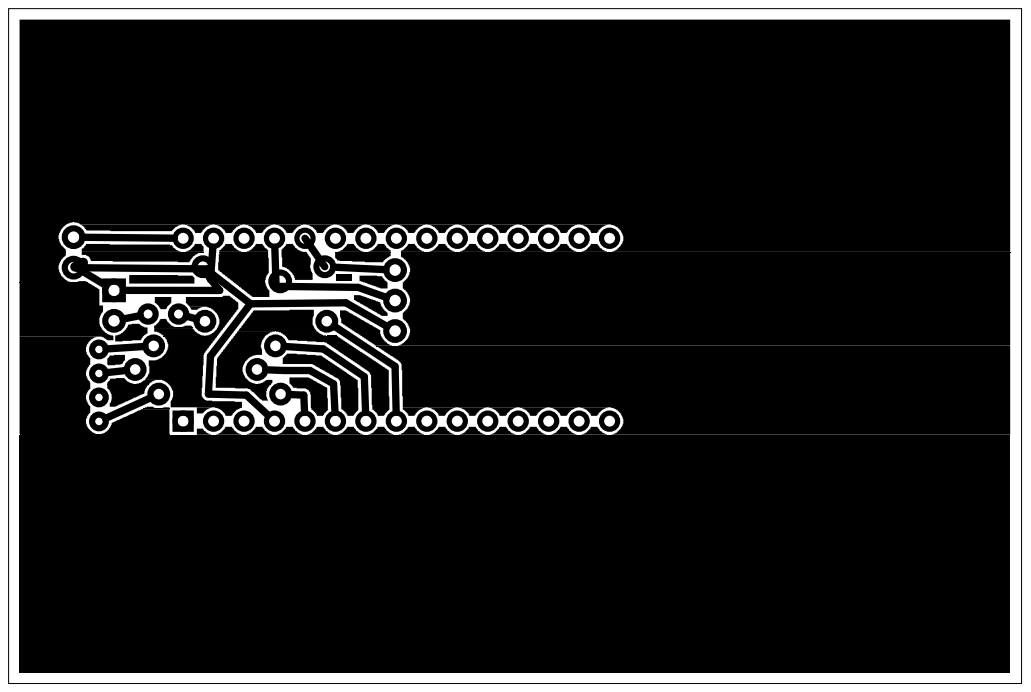
[picture p71: page 1]
