reseauducommun/cociclo/cociclo_Mexico/hardware/mexico/mexicoDF/cociclo_mexico_etch_copper_top_mirror.pdf

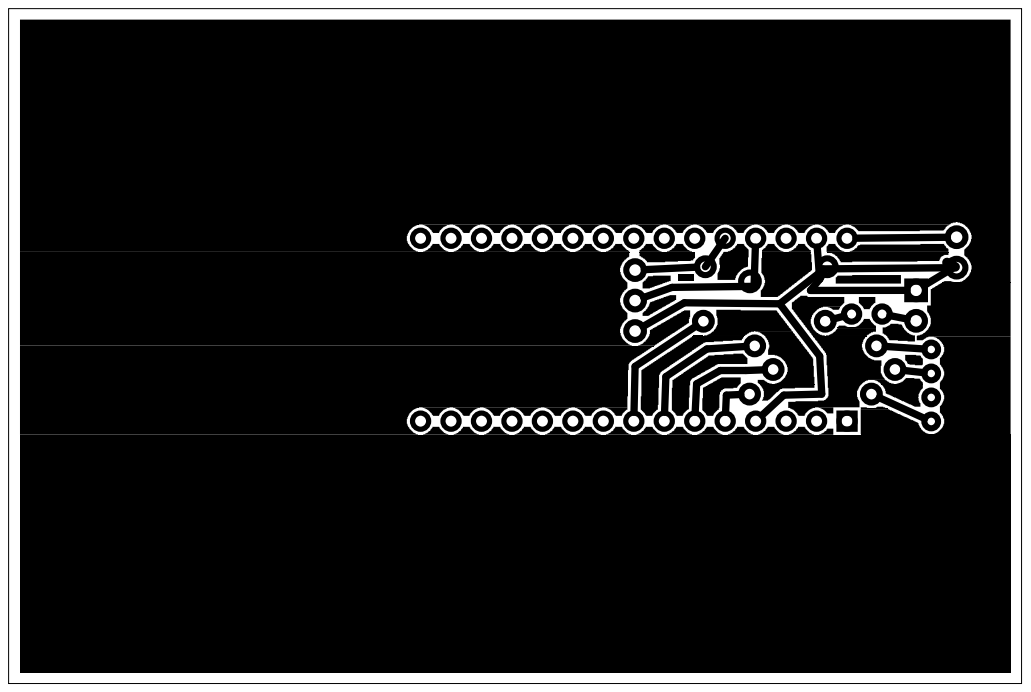
[picture p72: page 1]
