reseauducommun/cociclo/cociclo_Mexico/hardware/mexico/mexicoDF/cociclo_mexico_etch_mask_bottom.pdf

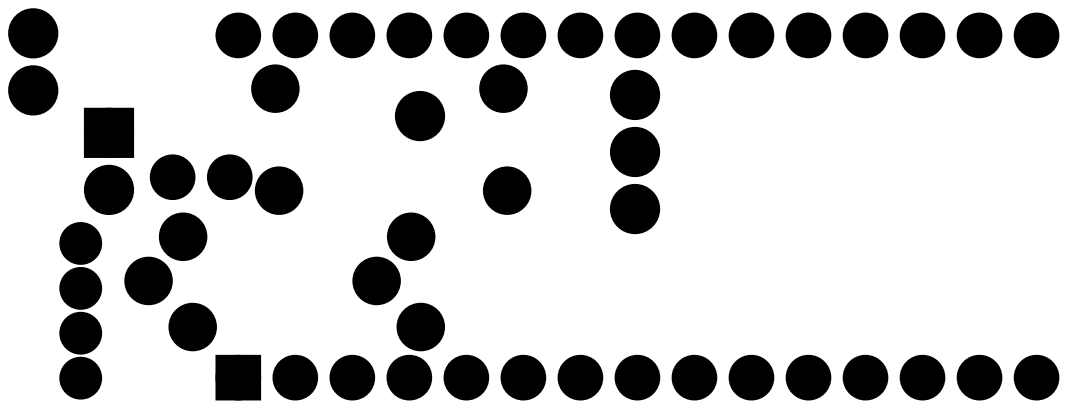
[picture p73: page 1]
