reseauducommun/cociclo/cociclo_Mexico/hardware/mexico/mexicoDF/cociclo_mexico_etch_mask_bottom_mirror.pdf

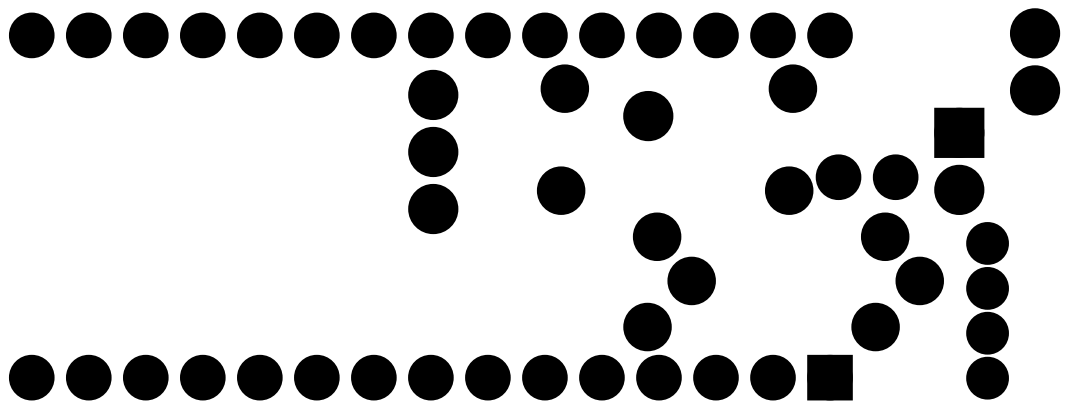
[picture p74: page 1]
