reseauducommun/cociclo/cociclo_Mexico/code/cociclo_cordova/www/img/logo.pdf

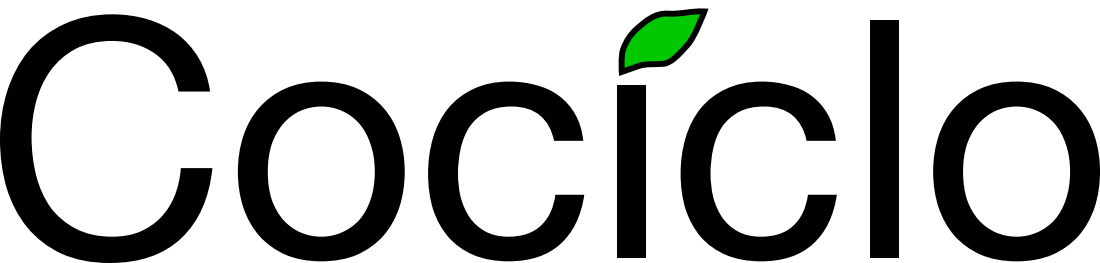
[picture p75: page 1]
