reseauducommun/cociclo/cociclo_05/software/cociclo_05/y_CREDITS.ino

/************* GEOLOCALISATION **************************************
  This is the code for Fetching your location from Google Geolocation API
  
  This code is provided by 
  techiesms
*********************************************************************/

// mercis à :

// artengine
// UQAM - École des arts visuels et médiatiques
// Le FabLab du PEC
// Perte de Signal
// UN/LOQUER

///////////////// PMS 3000 ////////////////////////////////////////////

//******************************
 //*Abstract: Read value of PM1,PM2.5 and PM10 of air quality
 //*Product Link: http://www.dfrobot.com.cn/goods-1113.html
 //*
 //*
 //*The RX pin on the sensor connects to pin D5 on the Wemnos D1 mini
 //*The TX pin on the sensor connects to pin D6 on the Wemnos D1 mini
 //
 //*Version：V3.1
 //*Author：Zuyang @ HUST
 //*Date：March.25.2016
 //******************************

 
