reseauducommun/cociclo/cociclo_05/software/cociclo_05/e_PMS3000.ino

/////// FONCTIONS PMS 3000 //////////

void pmsSensorRead(){

 if(PMSerial.find(0x42)){    
  
     PMSerial.readBytes(buf,LENG);
     // Serial.println(PMSerial.readBytes(buf,LENG));
     // Serial.println(buf[0]); 0x4d
    
 
    if(buf[0] == 0x4d){
     // if(checkValue(buf,LENG)){ // ne fonctionne pas
        PM01Value=transmitPM01(buf); //count PM1.0 value of the air detector module
        PM2_5Value=transmitPM2_5(buf);//count PM2.5 value of the air detector module
        PM10Value=transmitPM10(buf); //count PM10 value of the air detector module 
     // }           
    } 
  }

  static unsigned long OledTimer=millis();  
    if (millis() - OledTimer >=1000) 
    {
      OledTimer=millis(); 
      
      Serial.print("PM1.0: ");  
      Serial.print(PM01Value);
      Serial.println("  ug/m3");            
    
      Serial.print("PM2.5: ");  
      Serial.print(PM2_5Value);
      Serial.println("  ug/m3");     
      
      Serial.print("PM1 0: ");  
      Serial.print(PM10Value);
      Serial.println("  ug/m3");   
      Serial.println();
    }
}  /// fin de pmsSensorRead

char checkValue(unsigned char *thebuf, char leng)
{  
  char receiveflag=0;
  int receiveSum=0;

  for(int i=0; i<(leng-2); i++){
  receiveSum=receiveSum+thebuf[i];
  }
  receiveSum=receiveSum + 0x42;
 
  if(receiveSum == ((thebuf[leng-2]<<8)+thebuf[leng-1]))  //check the serial data 
  {
    receiveSum = 0;
    receiveflag = 1;
  }
  return receiveflag;
}

int transmitPM01(unsigned char *thebuf)
{
  int PM01Val;
  PM01Val=((thebuf[3]<<8) + thebuf[4]); //count PM1.0 value of the air detector module
  return PM01Val;
}

//transmit PM Value to PC
int transmitPM2_5(unsigned char *thebuf)
{
  int PM2_5Val;
  PM2_5Val=((thebuf[5]<<8) + thebuf[6]);//count PM2.5 value of the air detector module
  return PM2_5Val;
  }

//transmit PM Value to PC
int transmitPM10(unsigned char *thebuf)
{
  int PM10Val;
  PM10Val=((thebuf[7]<<8) + thebuf[8]); //count PM10 value of the air detector module  
  return PM10Val;

}

/////// FIN DES FONCTIONS PMS 3000 ///////////
