reseauducommun/cociclo/cociclo_05/software/cociclo_05/z_TODO.ino

// À faire  prendre n'importe quoi au-dessus de 30 ou encore prendre la meilleure résolution des 20 premières lectures
//
// utiliser les valeurs de lat et long comme variable, stocket celles-ci dans la mémoire
// refaire cette routine à chaque fois ré-initialisation du cociclo
// comment on ajoute des pages qui sont appelées par le code? Des include?

//// ajouter l'info pour le pms3000 dans la base de données
